khalidrh/4bit-ALU-With-Shift-unit/4bit-alu-with-shifter/images -schematic and layout/4bit-ALS-unit.png

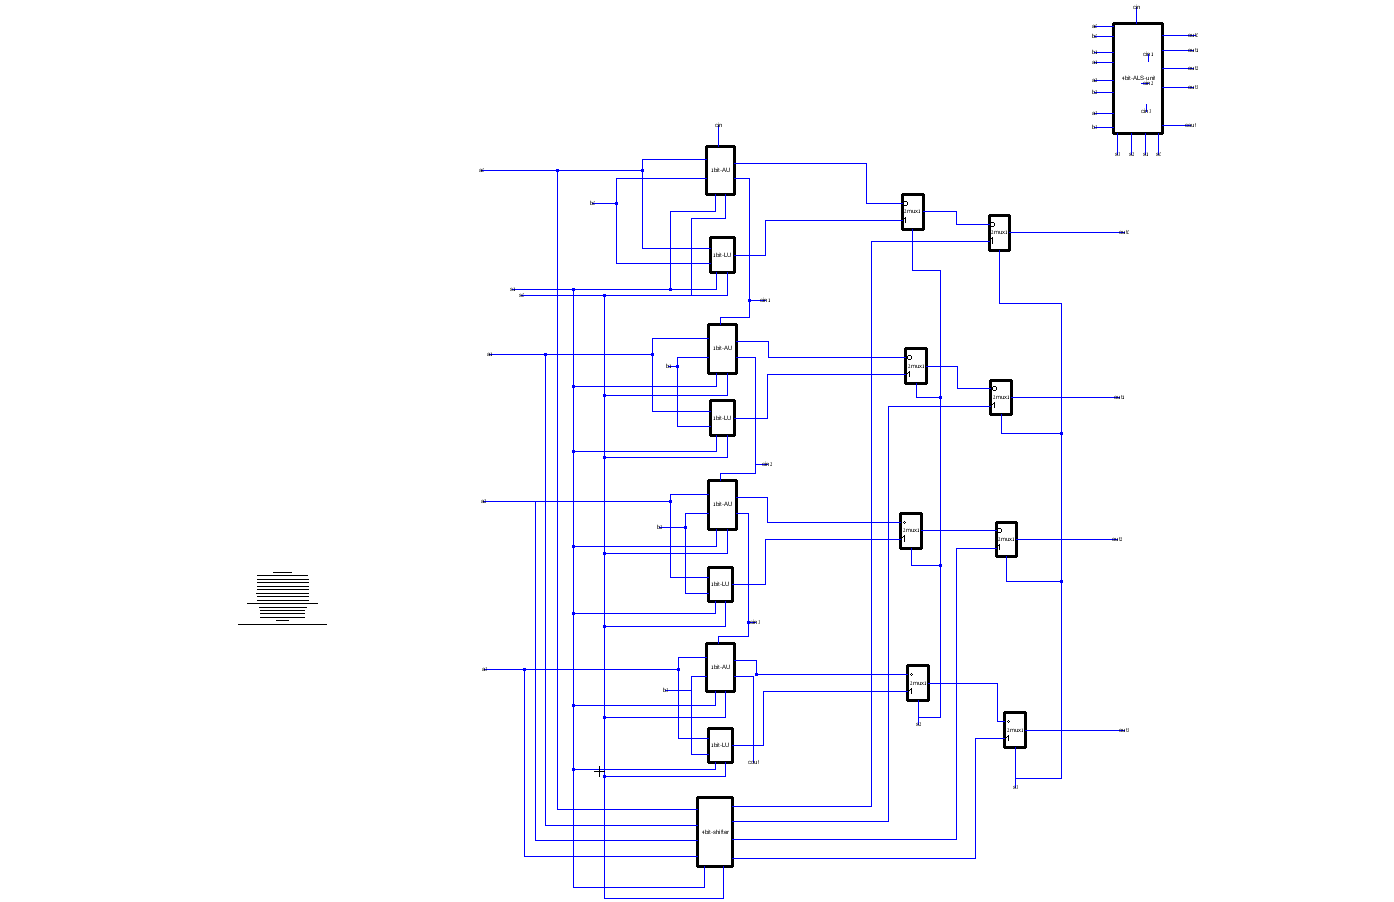
4bit-alu-with-shifter/images -schematic and layout/4bit-ALS-unit.png
