khalidrh/4bit-ALU-With-Shift-unit/4bit-alu-with-shifter/images -schematic and layout/4bit-shifter.png

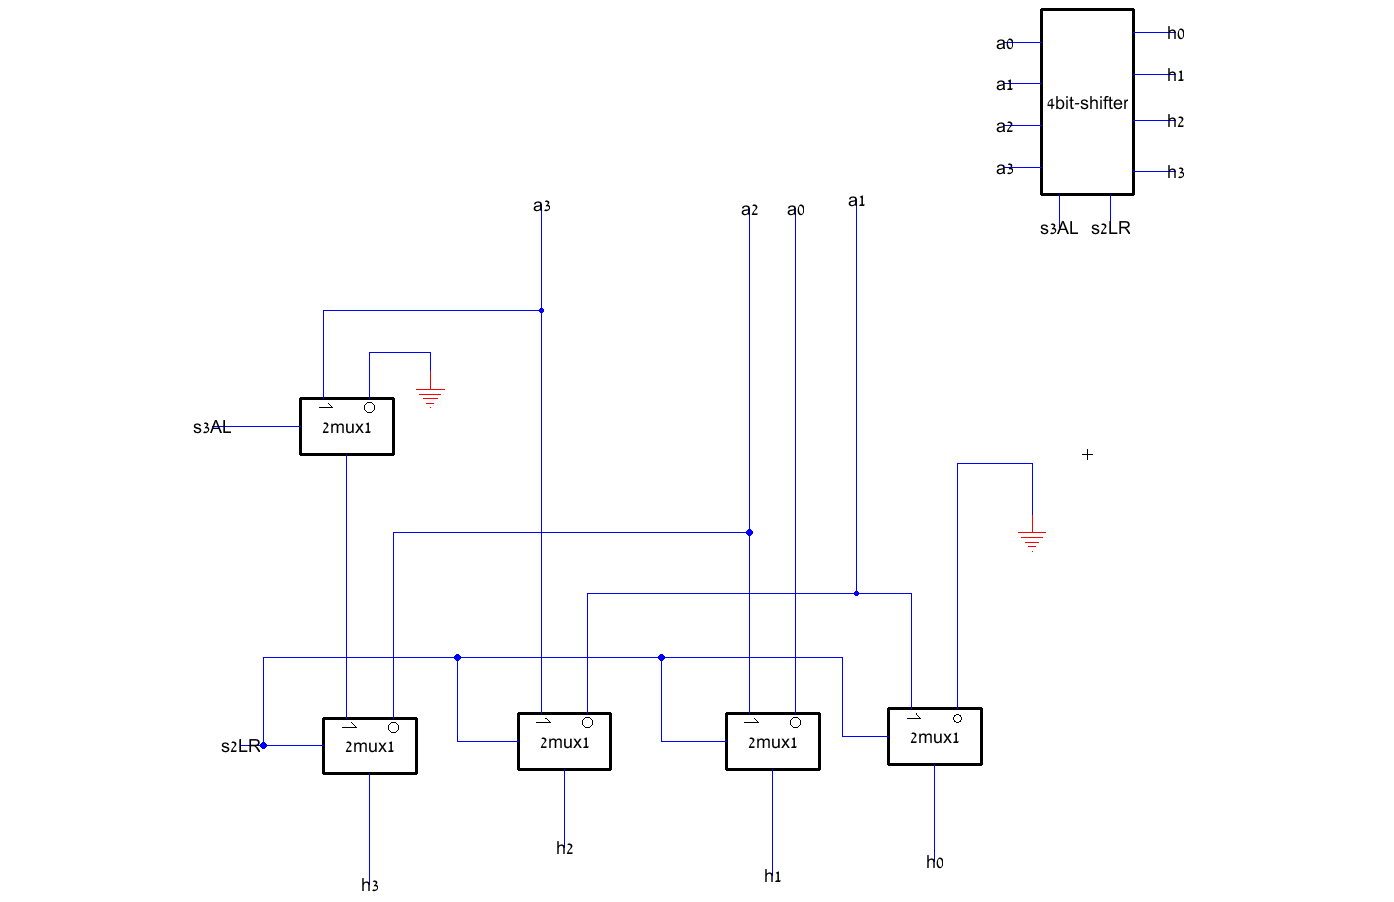
4bit-alu-with-shifter/images -schematic and layout/4bit-shifter.png
